AJMartel/Fuel-Rod-Prop/fuel rods png.png

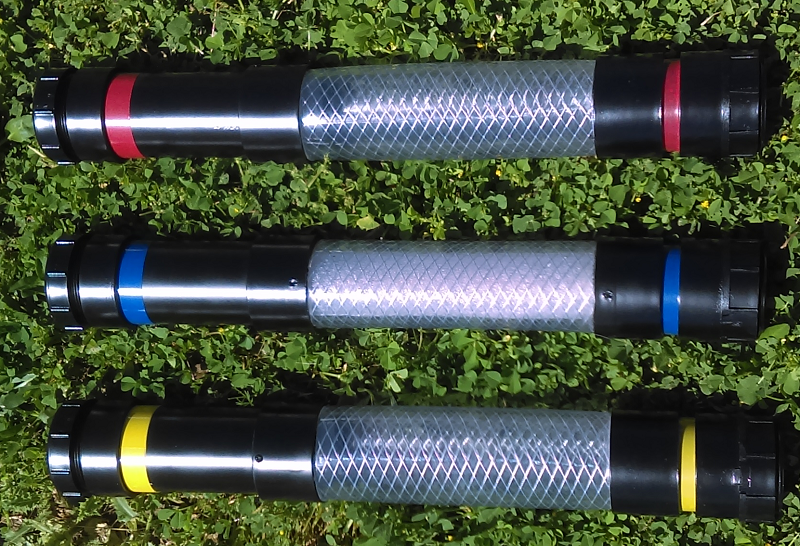
fuel rods png.png
