AJMartel/Fuel-Rod-Prop/IMAG0157.jpg

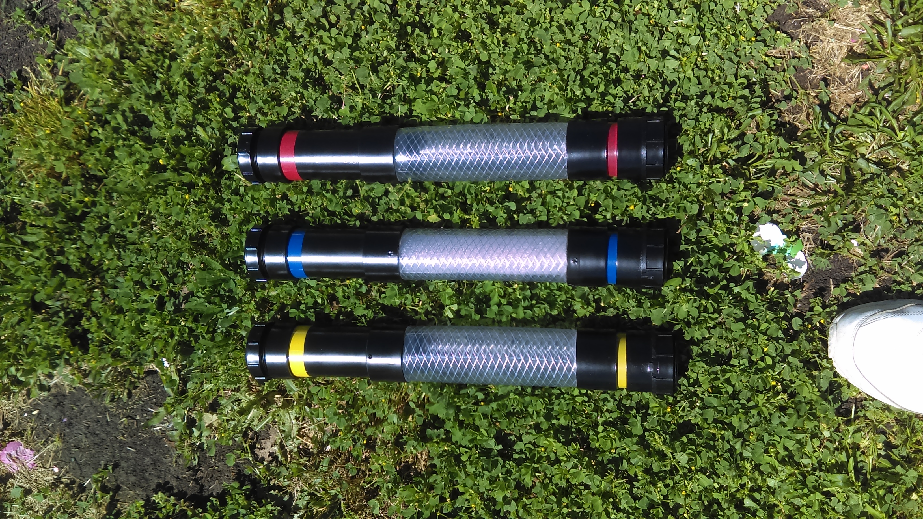
IMAG0157.jpg
