AJMartel/Fuel-Rod-Prop/IMAG0158.jpg

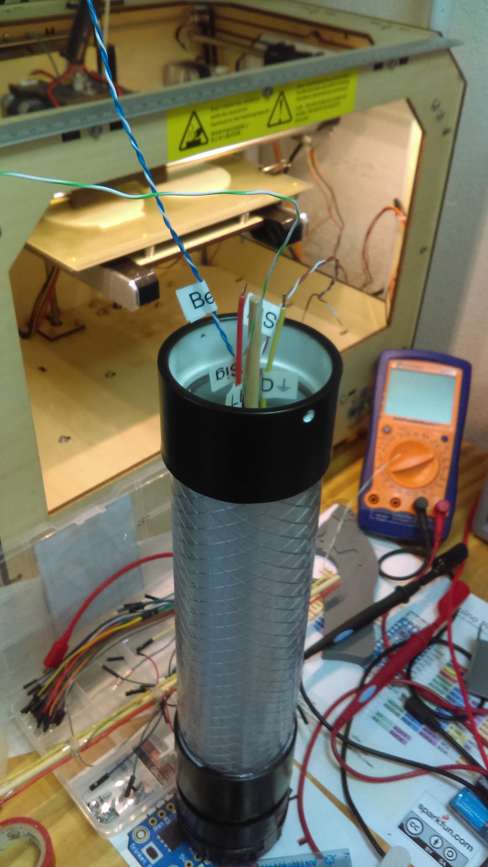
IMAG0158.jpg
