AJMartel/Fuel-Rod-Prop/IMAG0159.jpg

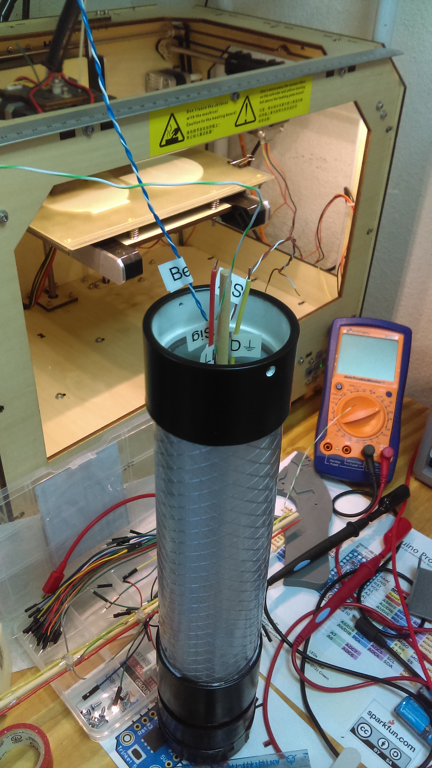
IMAG0159.jpg
