AJMartel/Fuel-Rod-Prop/IMAG0160.jpg

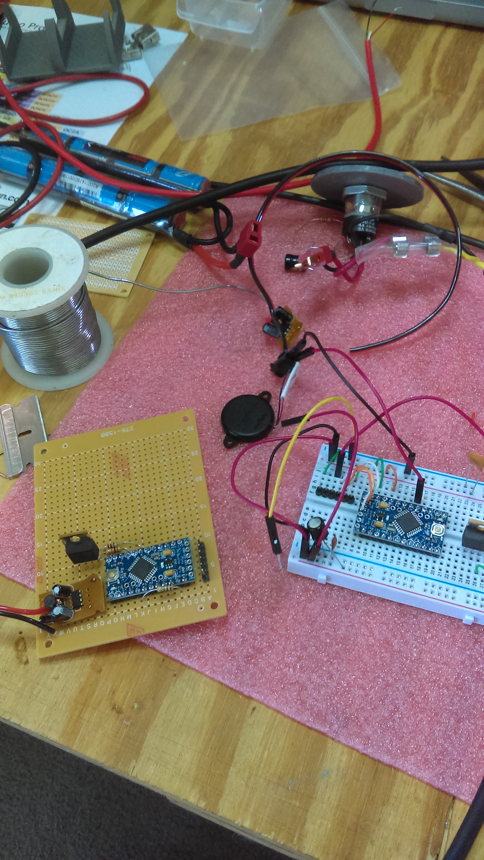
IMAG0160.jpg
