AJMartel/Fuel-Rod-Prop/IMAG0167.jpg

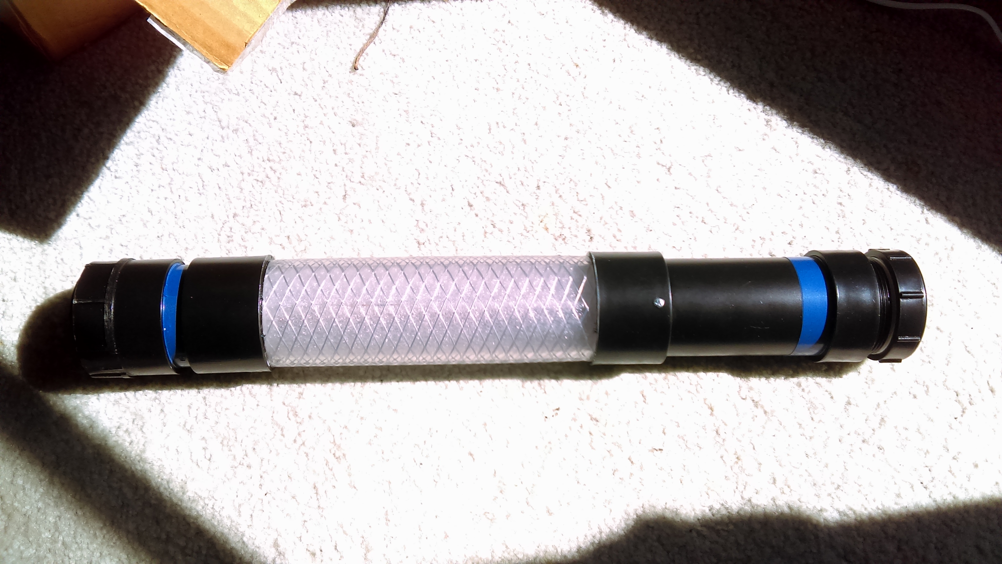
IMAG0167.jpg
