AJMartel/Fuel-Rod-Prop/IMAG0168.jpg

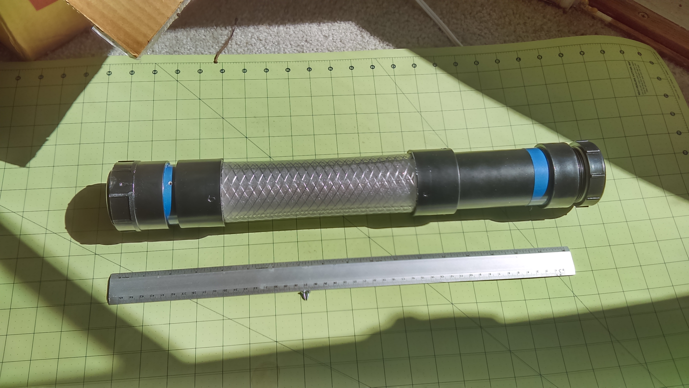
IMAG0168.jpg
