AJMartel/Fuel-Rod-Prop/IMAG0171.jpg

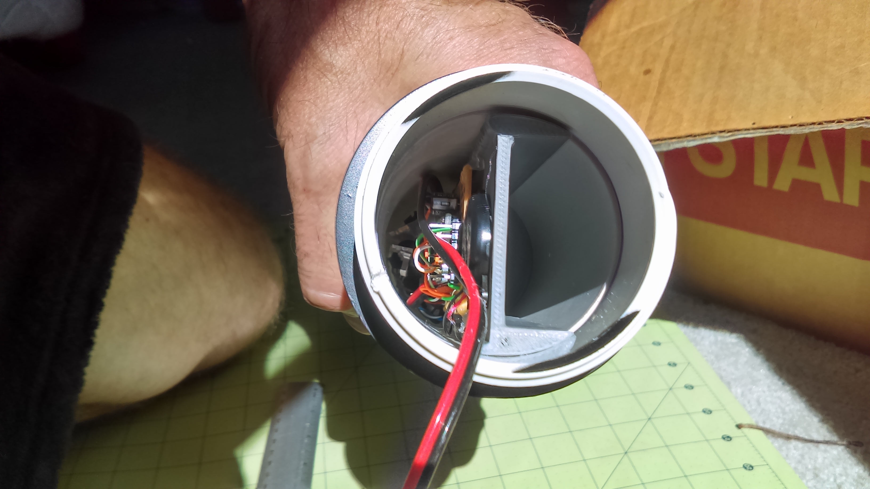
IMAG0171.jpg
