AJMartel/Fuel-Rod-Prop/IMAG0172.jpg

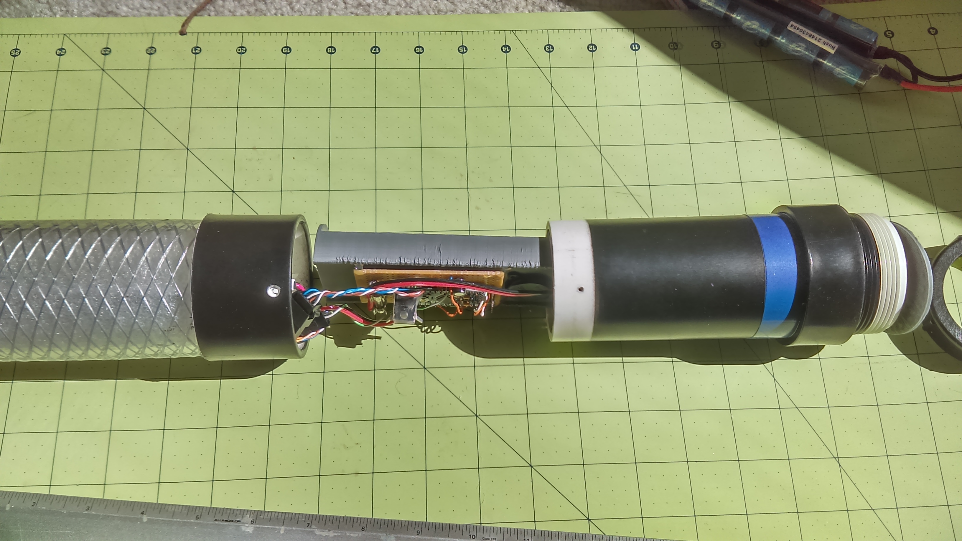
IMAG0172.jpg
