AJMartel/Fuel-Rod-Prop/IMAG0173.jpg

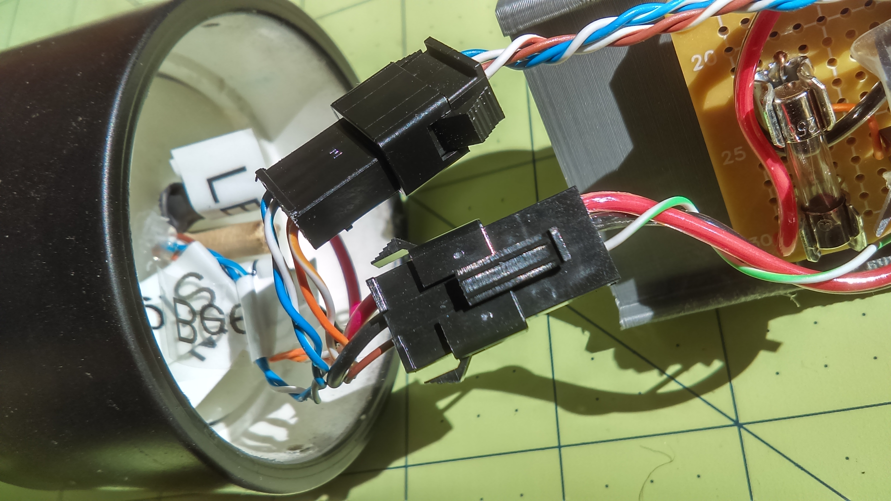
IMAG0173.jpg
