AJMartel/Fuel-Rod-Prop/IMAG0175.jpg

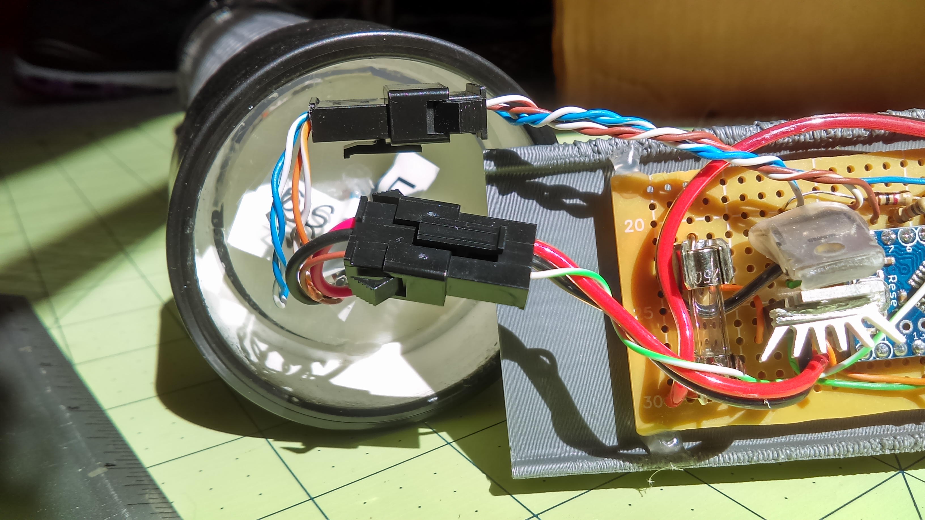
IMAG0175.jpg
