AJMartel/Fuel-Rod-Prop/IMAG0177.jpg

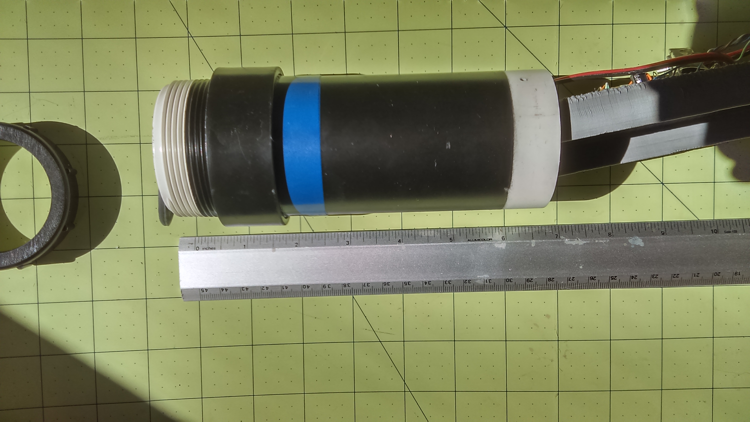
IMAG0177.jpg
